sparkfun/SparkFun_RTK_mosaic-X5/docs/mining-onocoy.md

---
icon: fontawesome/solid/sack-dollar
status: new
---

Some RTK networks, such as [Onocoy](https://www.onocoy.com/), offer users incentives for operating a reference station and contributing RTK corrections to their network. These incentives are often tied to a form of cryptocurrency, which is rewarded based upon a performance scale after the data is validated.

!!! warning
	This section is for educational purposes only!

	This section doesn't contain nor should it be represented as an endorsement of any of the projects mentioned nor as financial advice. Don’t invest anything you aren’t willing to lose.

## Onocoy Documentation
Onocoy provides users with documentation for [mining rewards](https://docs.onocoy.com/documentation/quick-start-guides/mine-rewards) with an RTK reference station. To get started, users will need to have installed and mounted the hardware of their RTK mosaic-X5 and created a user account with Onocoy. Then, users can [obtain NTRIP server credentials from their account](https://docs.onocoy.com/documentation/quick-start-guides/mine-rewards/3.-connect-your-station-to-onocoy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), to connect their reference station to the Onocoy network.

<figure markdown>
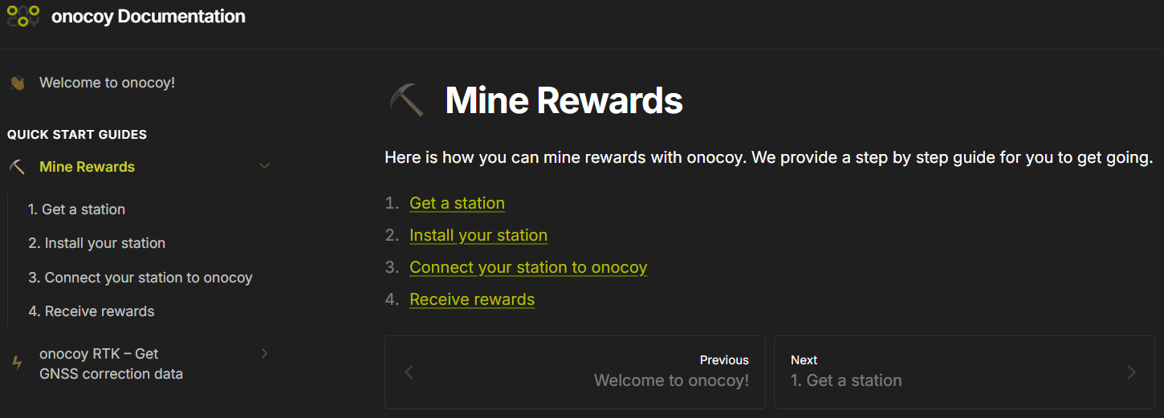
[picture p62: docs/assets/img/hookup_guide/onocoy-docs.png]
Onocoy documentaion

<figcaption markdown>Onocoy documentaion for [mining rewards](https://docs.onocoy.com/documentation/quick-start-guides/mine-rewards).</figcaption>
</figure>

## Configure the RTK mosaic-X5
In order to connect their RTK mosaic-X5 to the Onocoy network, users will need to adjust the configurations of the mosaic-X5 and setup an NTRIP server to the Onocoy network.

### :material-video-input-antenna: &nbsp;Enable L5 Band Reception
Before setting up the RTK mosaic-X5 as an NTRIP server, users will need to enable the GPS L5 frequency band in order to provide corrections for it. These steps, are documented in the [**Enable the L5 Band**](../L5/#l5-signal-reception) section of this tutorial:

<div class="grid cards" markdown>

-   **L5 Signal Reception**

	*Below, are instructions to enable the RTK mosaic-X5 to receive GNSS signals from the GPS L5 frequency band.*

	---

	--8<-- "./docs/L5.md:123:154"

</div>

### :material-router-network-wireless: &nbsp;Connect to the Onocoy Network
In order to connect the RTK mosaic-X5 to the Onocoy network, users will need to set up an NTRIP caster in the mosaic-X5 configuration settings. In order to receive the rewards, Onocoy expects a [specific set of configurations as listed in their online documentation](https://docs.onocoy.com/documentation/quick-start-guides/mine-rewards/3.-connect-your-station-to-onocoy).

<figure markdown>
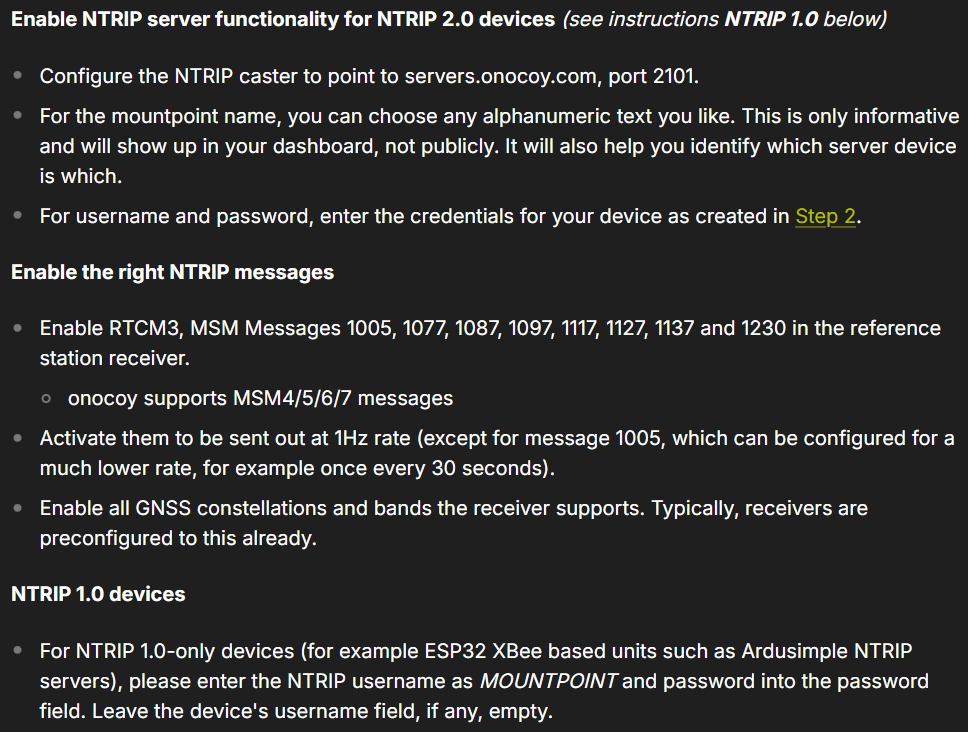
[picture p63: docs/assets/img/hookup_guide/onocoy-ntrip_settings.png]
NTRIP configuration settings

<figcaption markdown>The [specific parameters](https://docs.onocoy.com/documentation/quick-start-guides/mine-rewards/3.-connect-your-station-to-onocoy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) for connecting an NTRIP server to the Onocoy network, as listed in their documentation.</figcaption>
</figure>

Most of steps for these requirements, are documented in the [**Configure the NTRIP Server**](../ntrip_server/#configure-the-ntrip-server) section of this tutorial:

<div class="grid cards" markdown>

-   **Configure the NTRIP Server**

	---

	--8<-- "./docs/ntrip_server.md:49:55"

	??? failure "Ignore this information for this step"
		<s>
		--8<-- "./docs/ntrip_server.md:57:62"
		</s>

	!!! success
		Instead of the *confirmation email*, use the information provided in the [Onocoy documentation](https://docs.onocoy.com/documentation/quick-start-guides/mine-rewards/3.-connect-your-station-to-onocoy):

		> - Configure the NTRIP caster to point to `servers.onocoy.com`, port `2101`.
		> - For the `mountpoint` name, you can choose any alphanumeric text you like. This is only informative and will show up in your dashboard, not publicly. It will also help you identify which server device is which.
		> - For `username` and `password`, enter the credentials for your device as created in [Step 2](https://docs.onocoy.com/documentation/quick-start-guides/mine-rewards/3.-connect-your-station-to-onocoy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).

		<figure markdown>
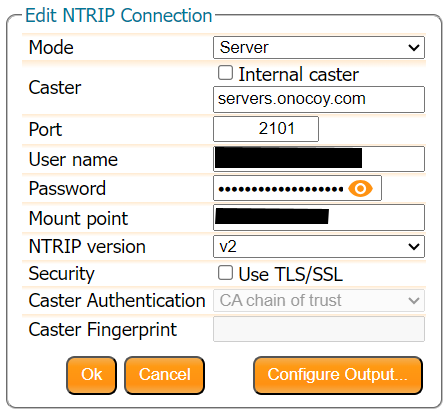
[picture p64: docs/assets/img/hookup_guide/onocoy-ntrip_server.png]
Configuring the NTRIP server
		
		<figcaption markdown>[Configuring the NTRIP server (PNG)](./assets/img/hookup_guide/onocoy-ntrip_server.png).</figcaption>
		</figure>

	--8<-- "./docs/ntrip_server.md:64:69"

	??? failure "Ignore this information for this step"
		<s>
		--8<-- "./docs/ntrip_server.md:71:76"
		</s>

	!!! success
		Instead, also select the RTCM messages listed in the [Onocoy documentation](https://docs.onocoy.com/documentation/quick-start-guides/mine-rewards/3.-connect-your-station-to-onocoy). Below, are the RTCM messages we selected:

		> - Enable RTCM3, MSM Messages `1005`, `1077`, `1087`, `1097`, `1117`, `1127`, `1137`, and `1230` in the reference station receiver.
		> - onocoy supports MSM4/5/6/7 messages

		<figure markdown>
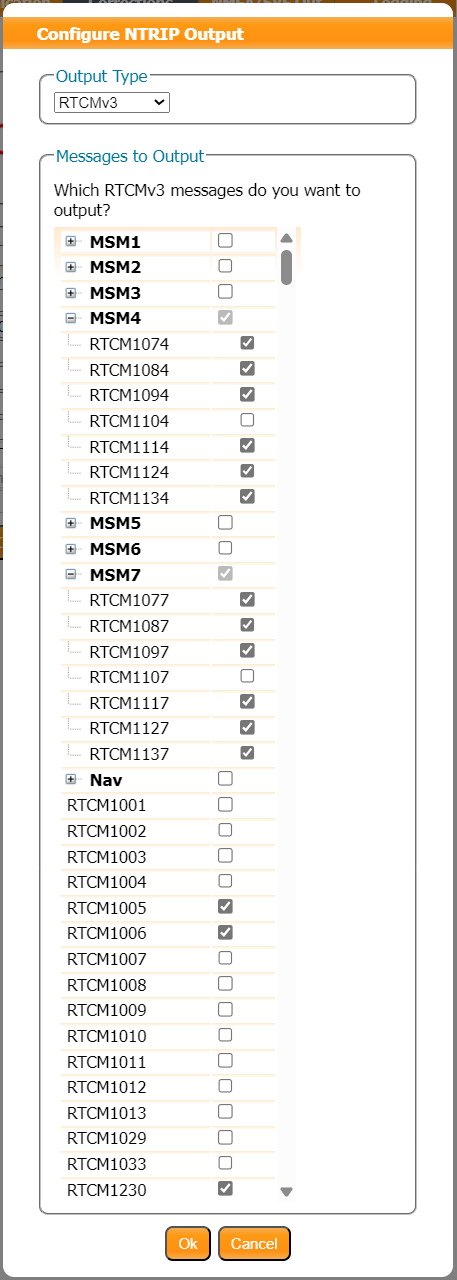
[picture p65: docs/assets/img/hookup_guide/onocoy-rtcm_messages.png]
RTCMv3 messages
		
		<figcaption markdown>[RTCMv3 messages (PNG)](./assets/img/hookup_guide/onocoy-rtcm_messages.png).</figcaption>
		</figure>

	--8<-- "./docs/ntrip_server.md:78:79"

</div>

### :fontawesome-solid-map-location-dot: &nbsp;Enable L5 Corrections
The last step in configuring the NTRIP server, users will need to enable the GPS L5 signal to be included in the MSM output messages. This will allow the RTK mosaic-X5 to provide RTK corrections for the GPS L5 frequency band. These steps, are documented in the [**Output L5 Corrections**](../L5/#output-l5-corrections) section of this tutorial:

<div class="grid cards" markdown>

-   **Output L5 Corrections**

	*Below, are instructions for outputting RTK corrections for the GPS L5 frequency band, from the RTK mosaic-X5.*

	---

	--8<-- "./docs/L5.md:167"

</div>

## :fontawesome-solid-money-bill-trend-up: &nbsp;Receive Rewards
Once users have connected the RTK mosaic-X5 as an NTRIP server on the Onocoy network, there are a few additional steps in that need to be completed, a specified in their [online documentation](https://docs.onocoy.com/documentation/quick-start-guides/mine-rewards/4.-receive-rewards).

<article style="text-align: center;" markdown>
:material-pickaxe::material-gold:&nbsp; Happy Mining! :material-pickaxe::material-gold:
</article>
