sparkfun/SparkFun_RTK_mosaic-X5/Front_Panel/RTK_mosaic-X5_Front_Panel.png

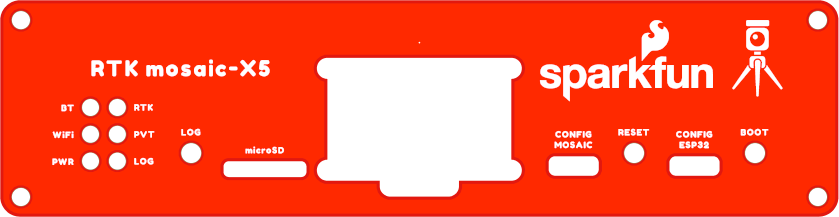
Front_Panel/RTK_mosaic-X5_Front_Panel.png
