sparkfun/SparkFun_RTK_mosaic-X5/Rear_Panel/RTK_mosaic-X5_Rear_Panel.png

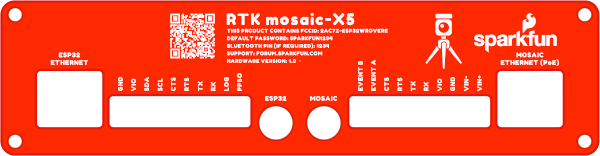
Rear_Panel/RTK_mosaic-X5_Rear_Panel.png
