sparkfun/SparkFun_RTK_mosaic-X5/docs/assets/img/hookup_guide/Log.jpg

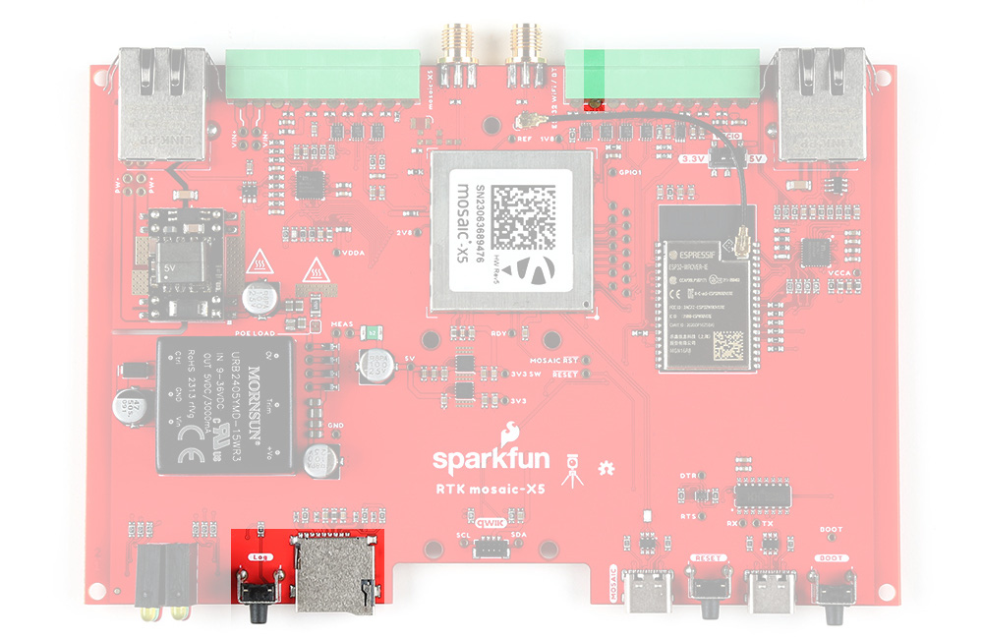
docs/assets/img/hookup_guide/Log.jpg
