sparkfun/SparkFun_RTK_mosaic-X5/docs/assets/img/hookup_guide/OLED2.png

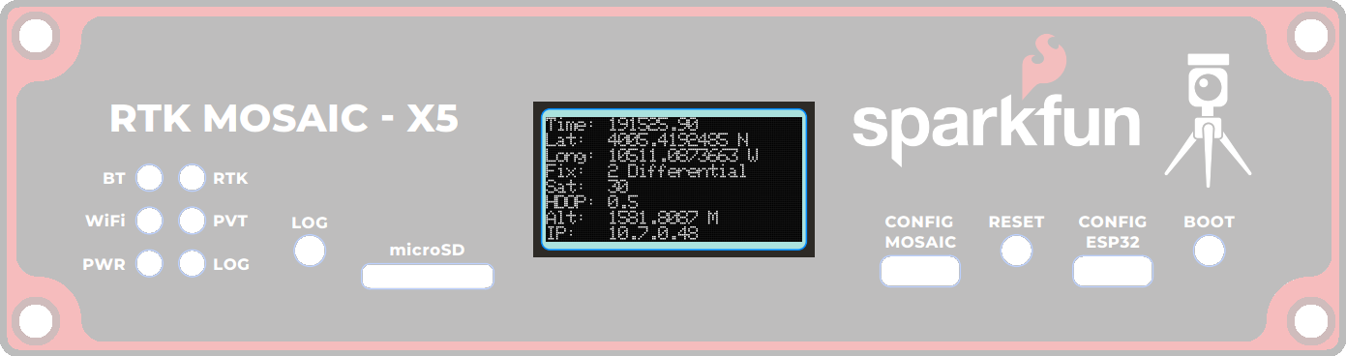
docs/assets/img/hookup_guide/OLED2.png
