sparkfun/SparkFun_RTK_mosaic-X5/docs/assets/img/hookup_guide/panel-front.png

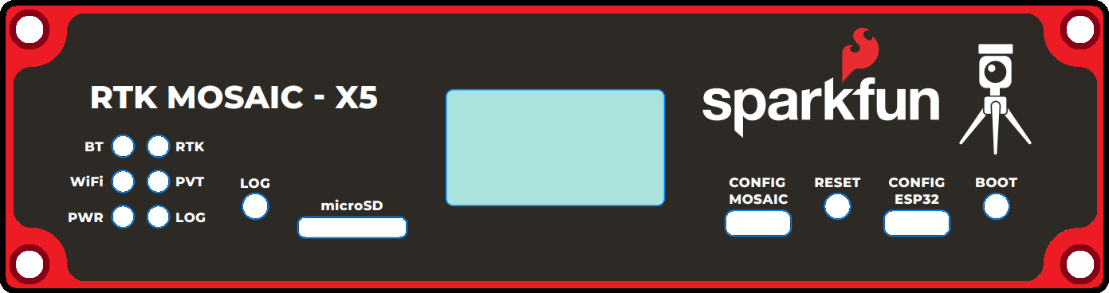
docs/assets/img/hookup_guide/panel-front.png
