sparkfun/SparkFun_RTK_mosaic-X5/docs/assets/img/hookup_guide/panel-rear.png

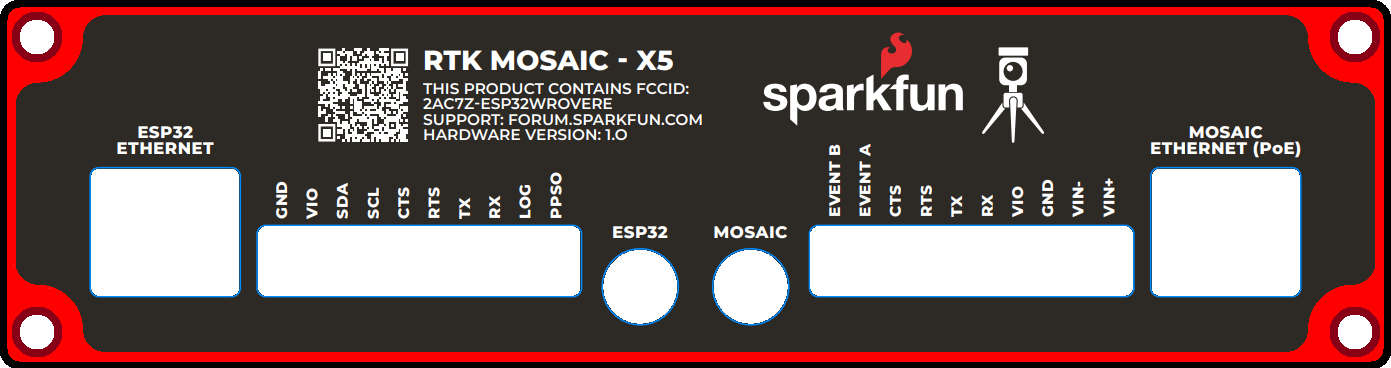
docs/assets/img/hookup_guide/panel-rear.png
