sparkfun/SparkFun_RTK_mosaic-X5/docs/assets/img/hookup_guide/PCB_Bottom.png

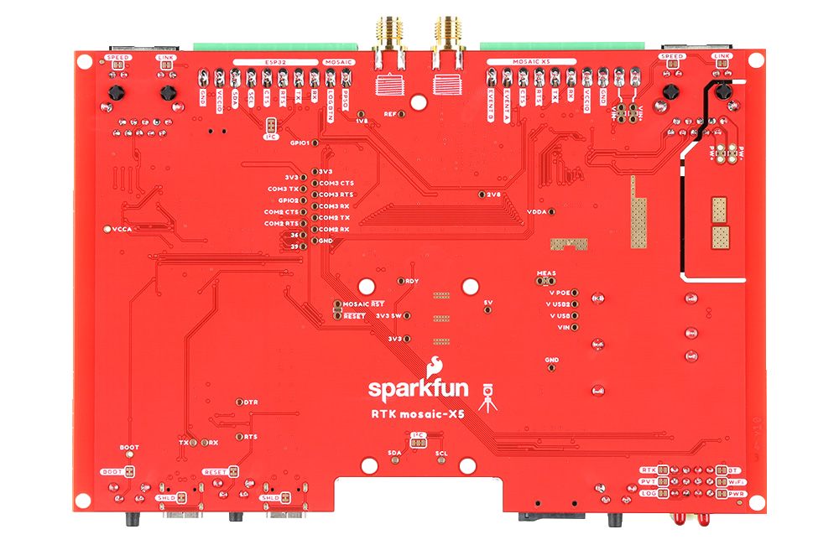
docs/assets/img/hookup_guide/PCB_Bottom.png
