sparkfun/SparkFun_RTK_mosaic-X5/docs/assets/img/hookup_guide/template_OLED-info.png

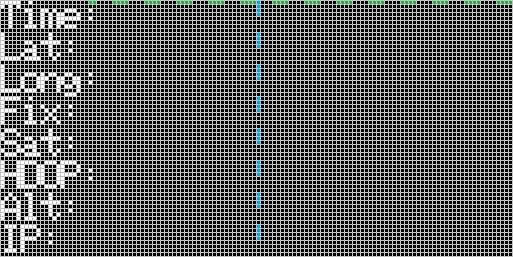
docs/assets/img/hookup_guide/template_OLED-info.png
