sparkfun/SparkFun_RTK_mosaic-X5/docs/assets/component_documentation/mowi_schematic_MERGED.pdf

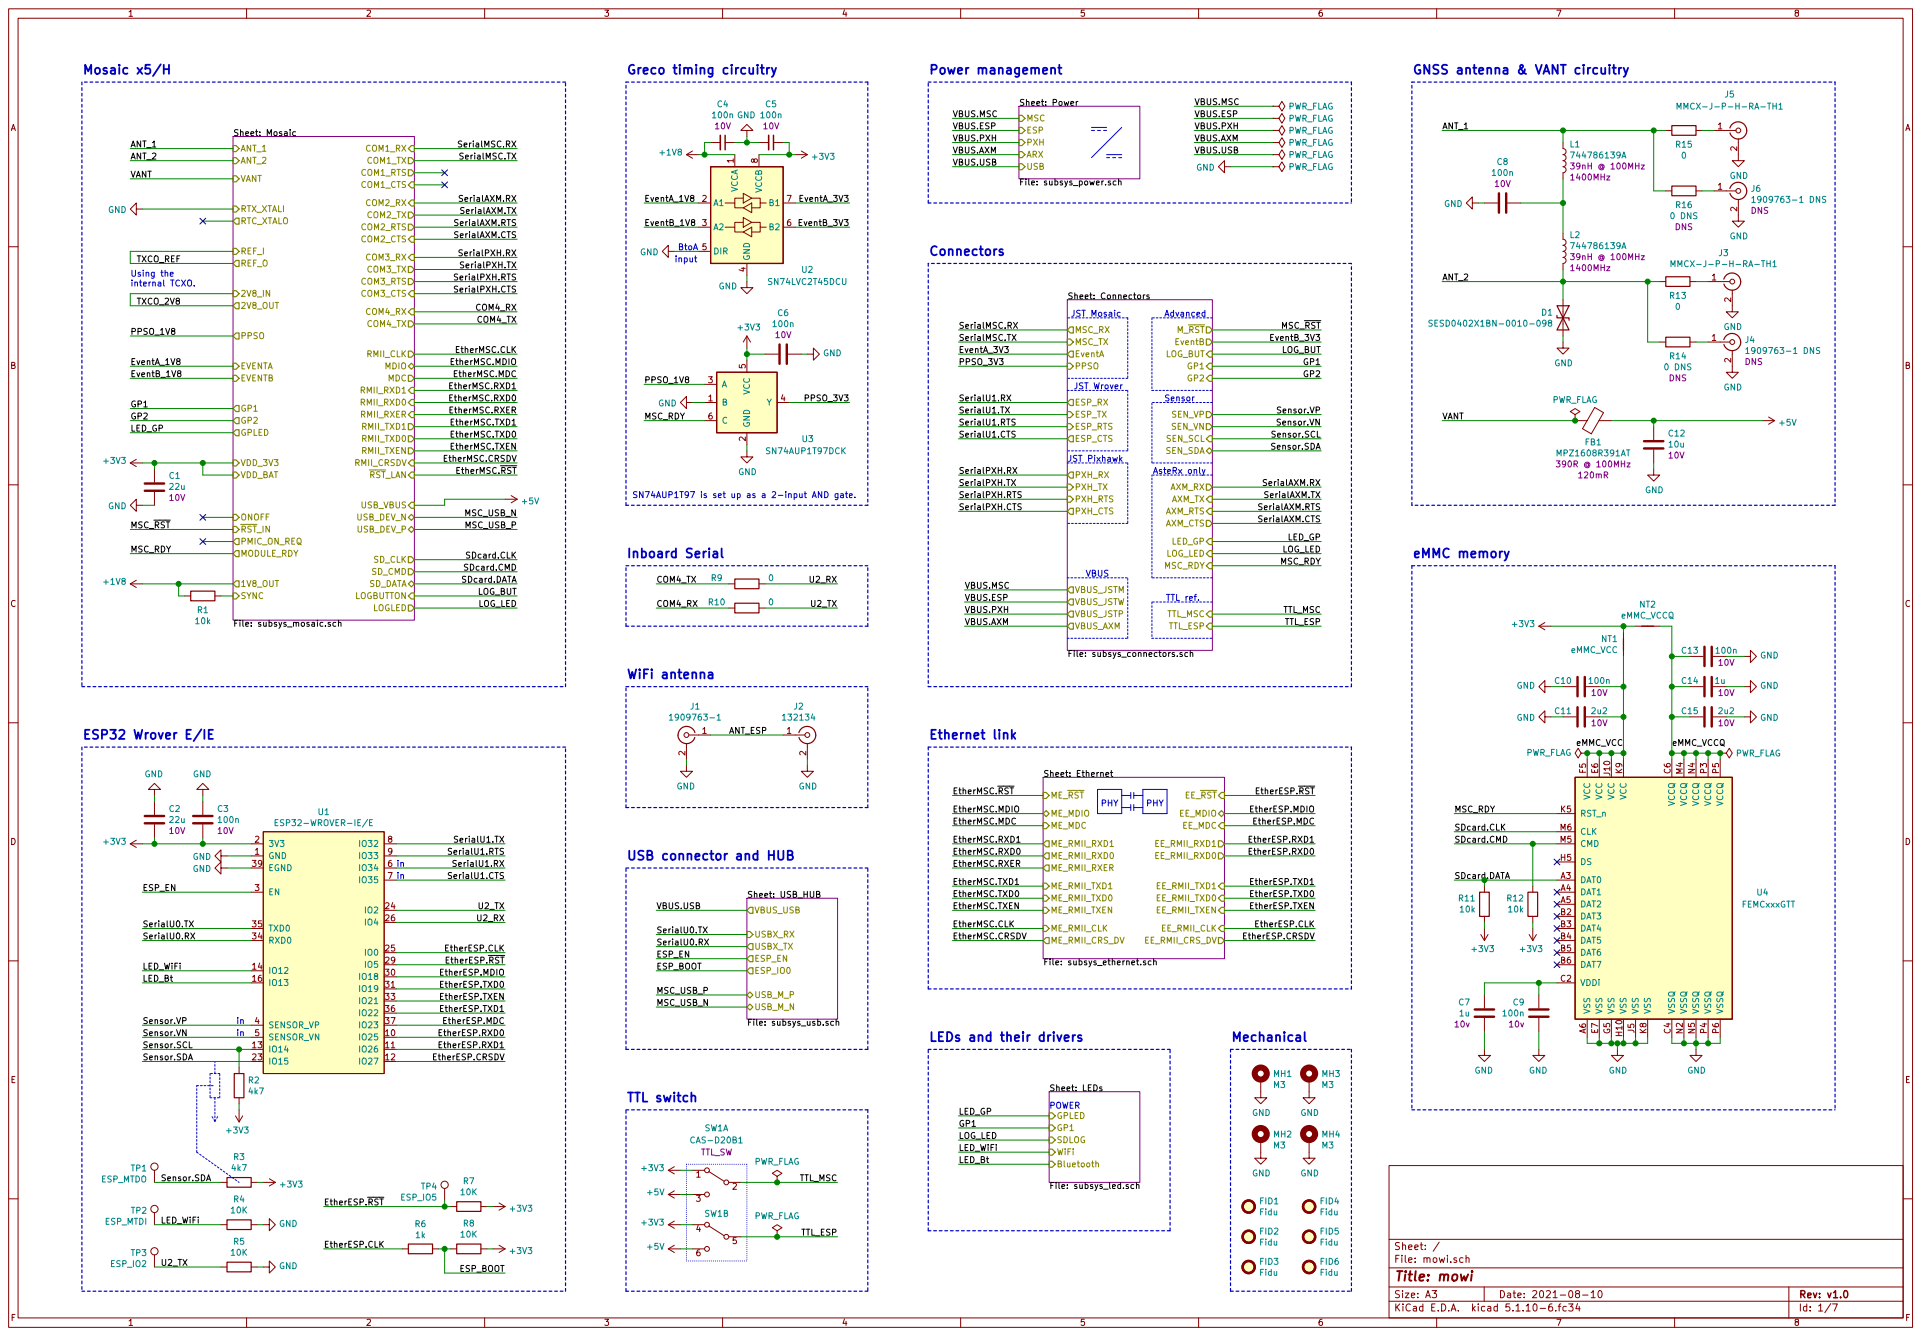
[picture p147: page 1]

Sheet: Mosaic File: subsys_mosaic.sch VDD_3V3 VDD_BAT REF_I 2V8_IN
VANT ANT_2 ANT_1 RTX_XTALI ONOFF RST_IN
COM4_TX COM3_RTS COM3_TX COM2_RTS COM2_TX COM1_RTS COM1_TX

GNSS antenna & VANT circuitry

Sheet: Power File: subsys_power.sch MSC

8 U2 SN74LVC2T45DCU
Advanced AsteRx only VBUS

J3 MMCX-J-P-H-RA-TH1 GND GND

SN74AUP1T97 is set up as a 2-input AND gate.
ESP_BOOT COM4_TX

TTL_MSC
TTL_ESP
Sheet: Ethernet File: subsys_ethernet.sch ME_RMII_TXEN ME_RMII_TXD0 ME_RMII_TXD1 ME_RMII_CLK
EtherESP.RST EtherESP.CRSDV

USB connector and HUB

EtherESP.RST EtherESP.MDC
EtherESP.MDIO

Sensor.VP
Sensor.SCL Sensor.VN

EtherESP.RXD1 EtherESP.RXD0 EtherESP.CRSDV

LEDs and their drivers

Sheet: LEDs File: subsys_led.sch Bluetooth WiFi GP1 GPLED

Id: 1/7 Title: mowi File: mowi.sch Sheet: /

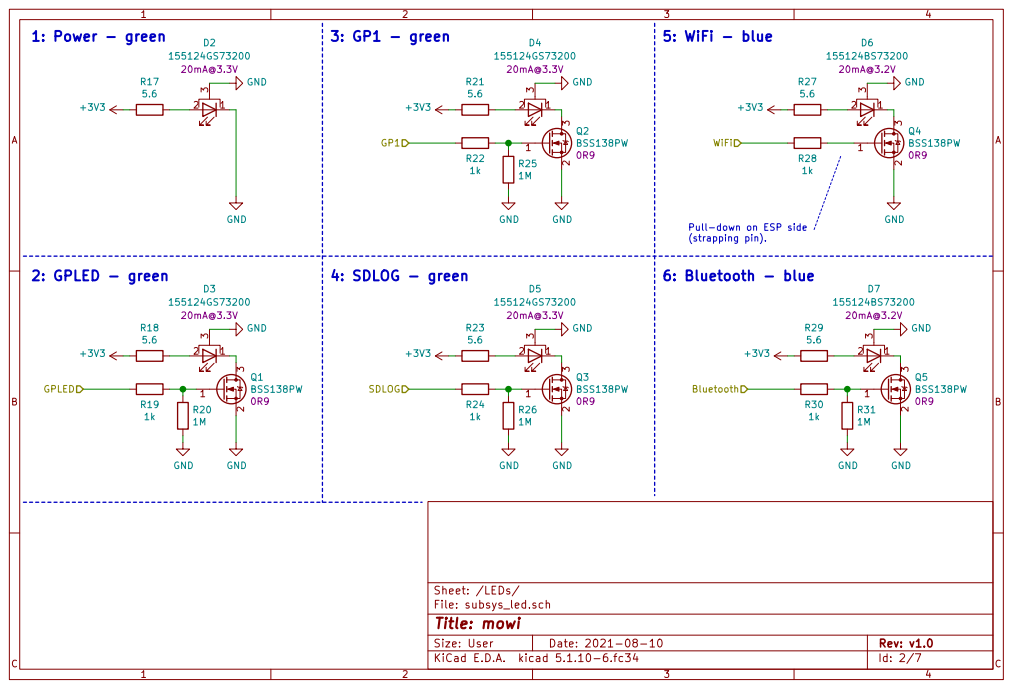
[picture p148: page 2]

Pull-down on ESP side
(strapping pin).

File: subsys_led.sch Sheet: /LEDs/ R19

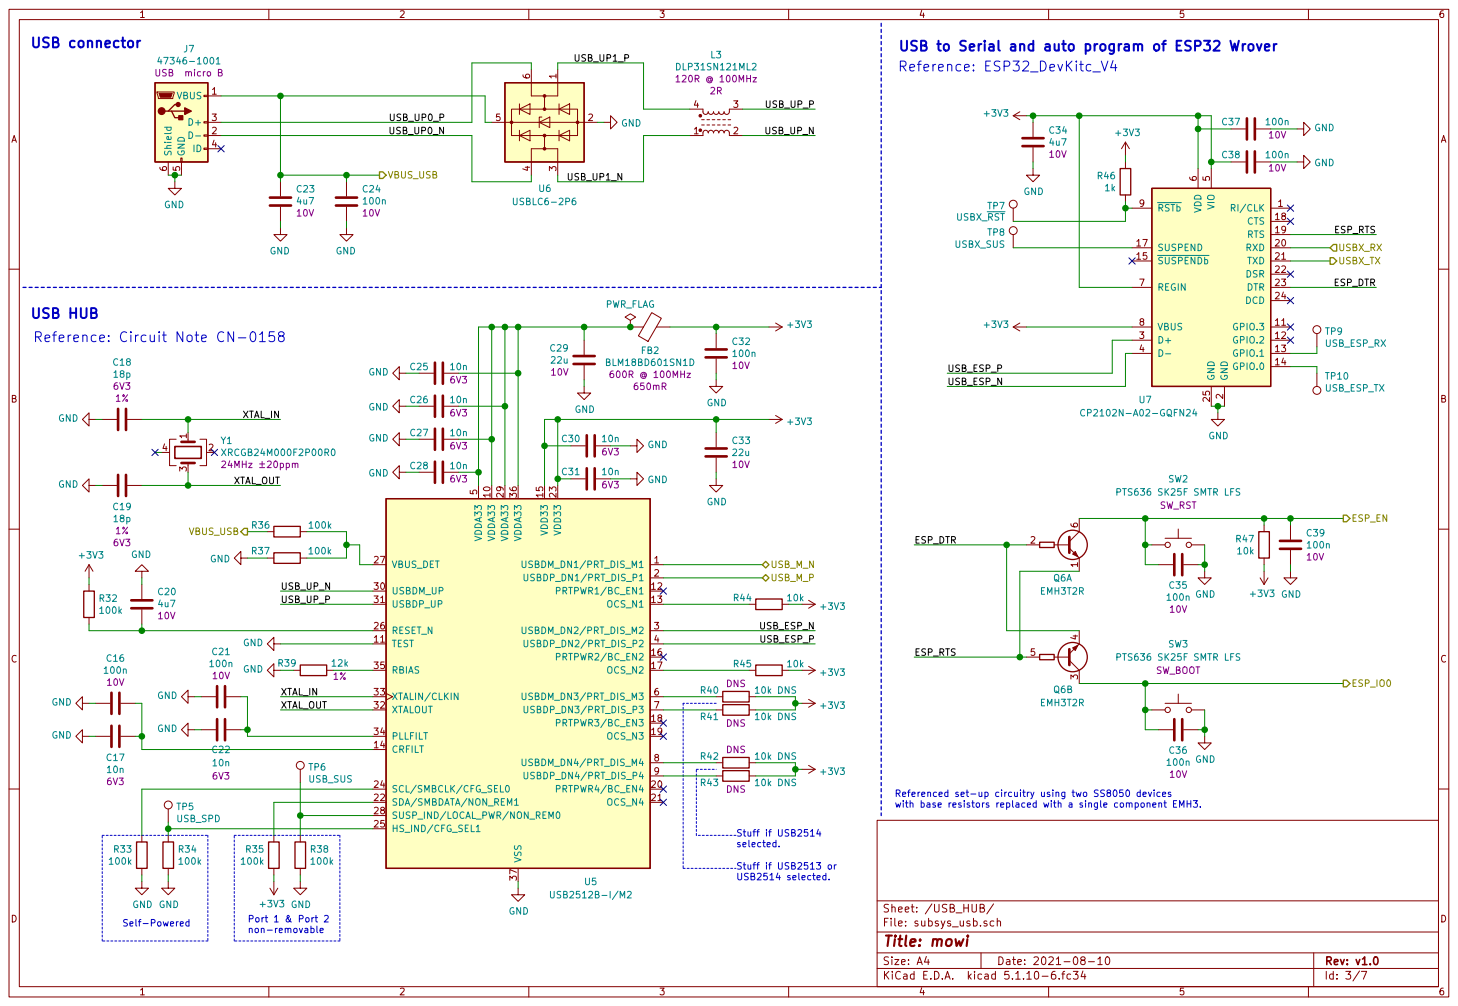
[picture p149: page 3]

non-removable Reference: Circuit Note CN-0158

6 REGIN 7 VBUS 8 RSTb 9U7 CP2102N-A02-GQFN24 GND

2 RXD 20 TXD 21 DSR 22 DTR 23 DCD 24 GND 25 D+ 3 D- 4 VIO

Referenced set-up circuitry using two SS8050 devices
with base resistors replaced with a single component EMH3.

Stuff if USB2513 or USB2514 selected.

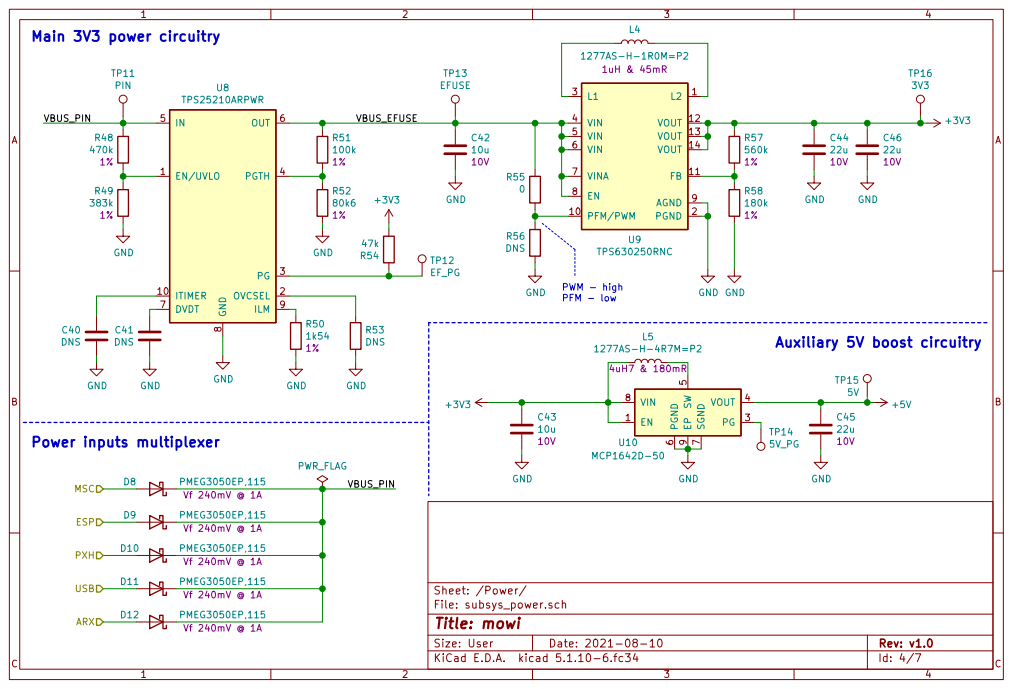
[picture p150: page 4]

PWM - high PFM - low Power inputs multiplexer

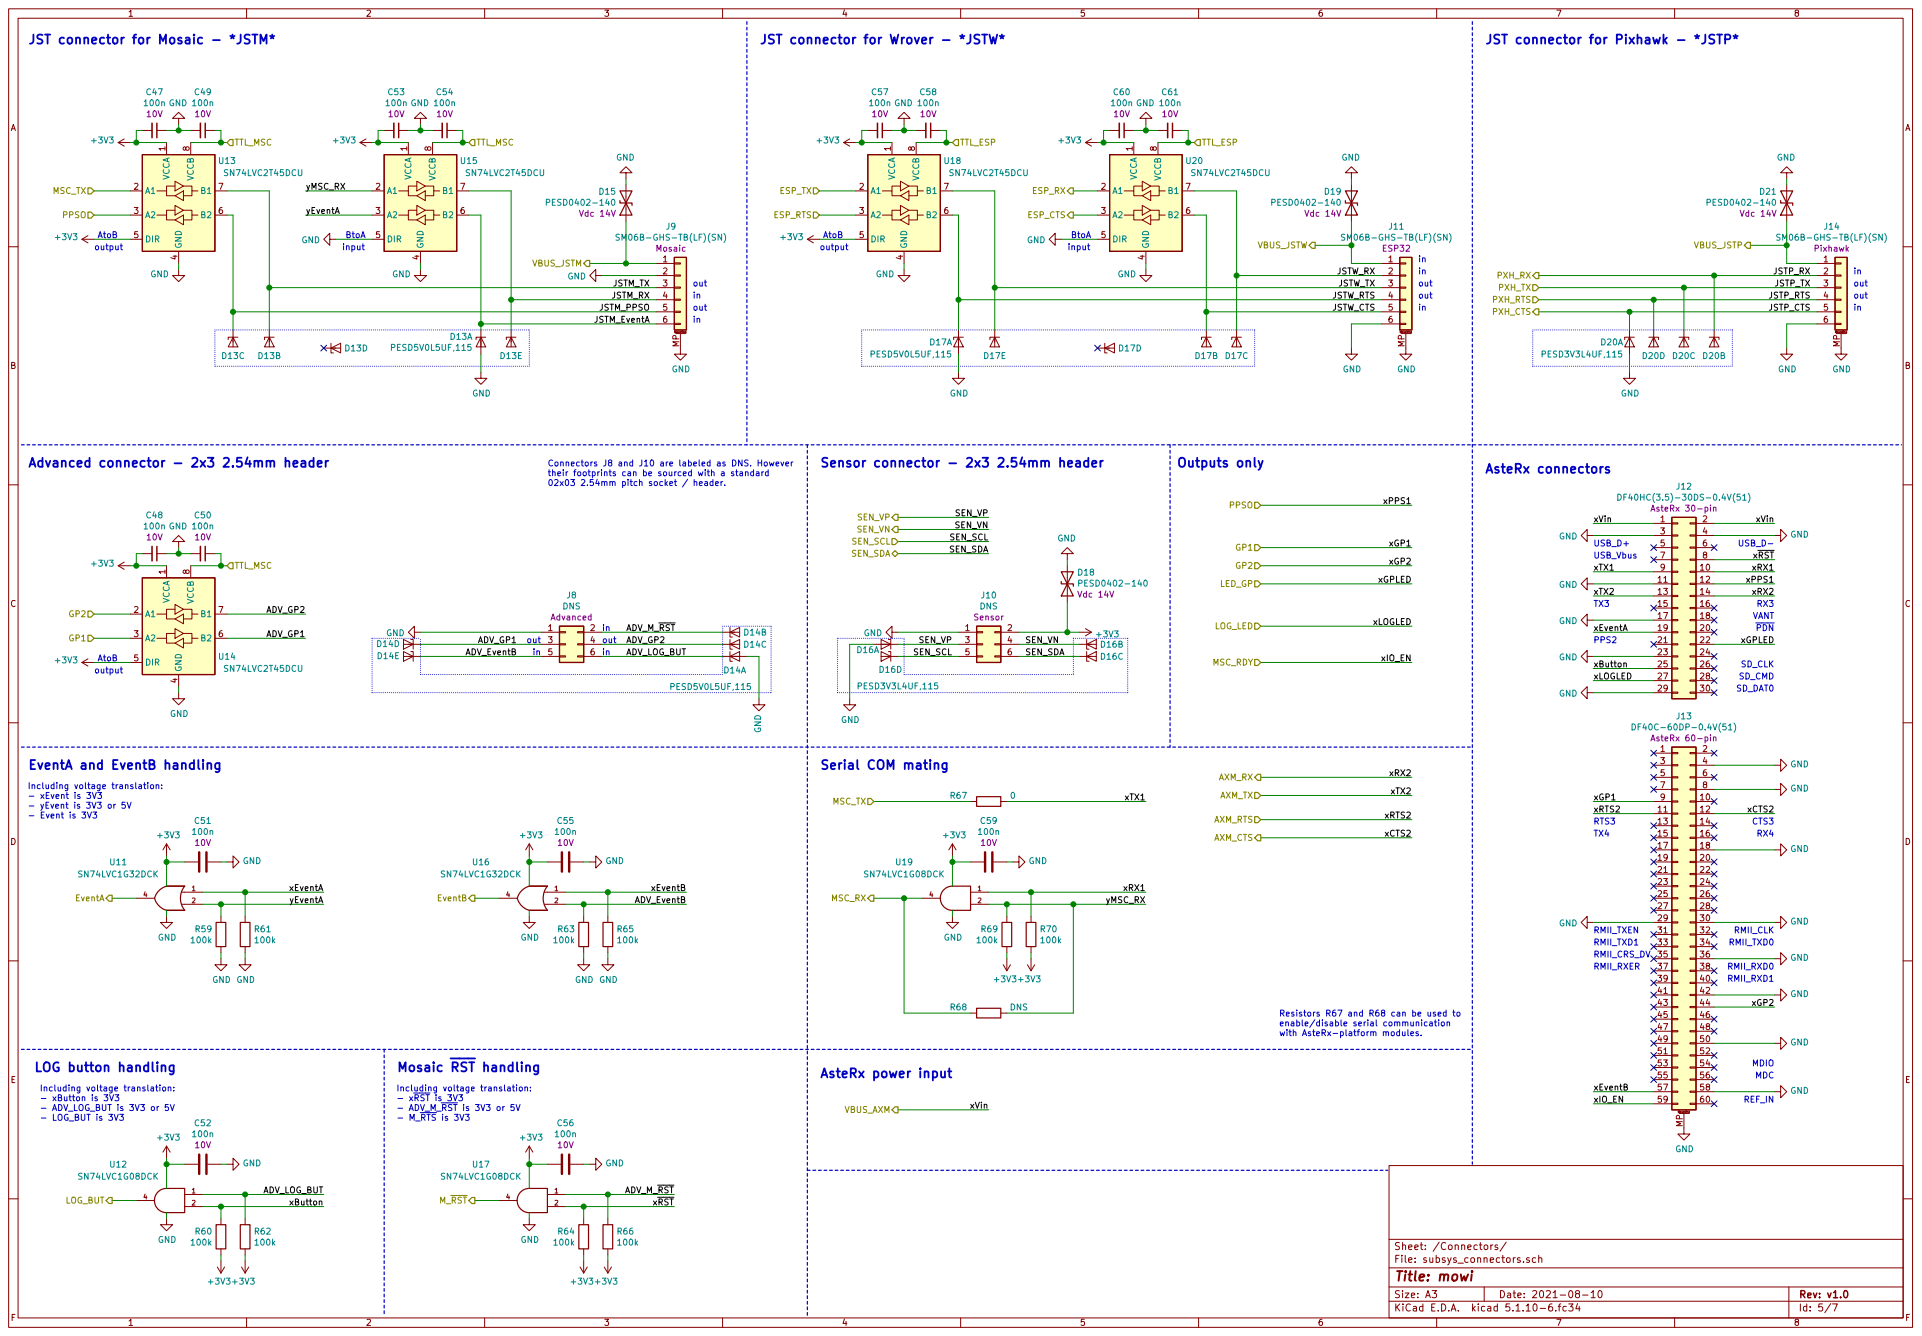
[picture p151: page 5]

JST connector for Mosaic - *JSTM*

JST connector for Pixhawk - *JSTP*

J14 SM06B-GHS-TB(LF)(SN) Pixhawk

02x03 2.54mm pitch socket / header. BtoA
input

out LOG button handling

AsteRx 60-pin GND GND

in Advanced connector - 2x3 2.54mm header AtoB

Connectors J8 and J10 are labeled as DNS. However
their footprints can be sourced with a standard

EventA and EventB handling

Including voltage translation: - xEvent is 3V3

enable/disable serial communication with AsteRx-platform modules.

Including voltage translation: - xButton is 3V3

Including voltage translation: - xRST is 3V3

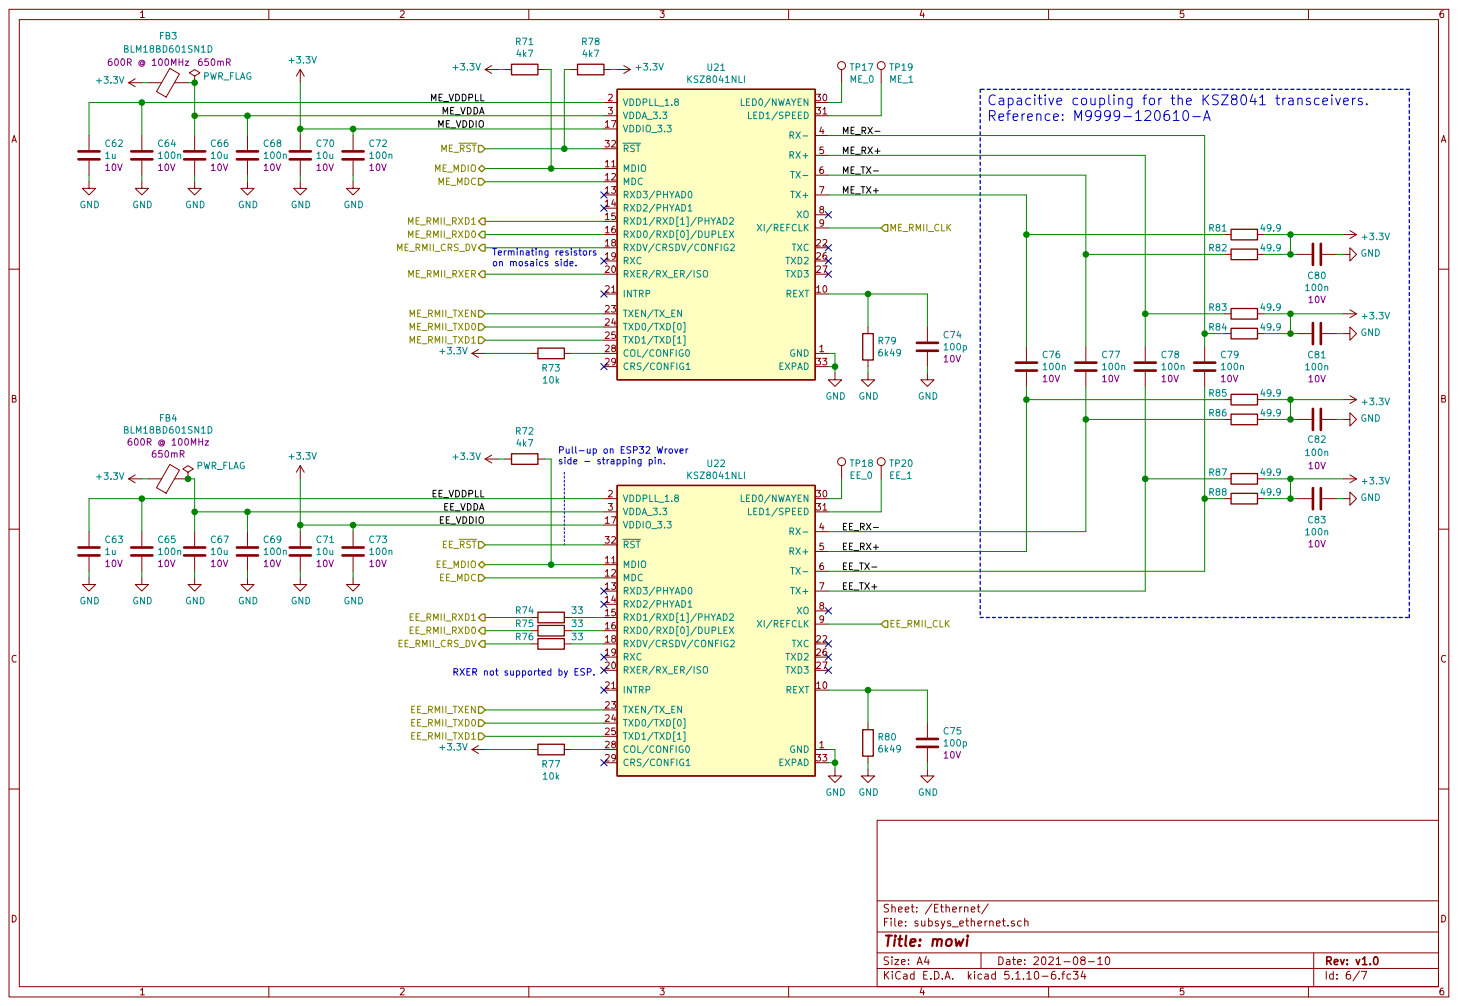
[picture p152: page 6]

EE_RST ME_MDC ME_RMII_CRS_DV ME_RMII_TXD0 ME_RMII_RXD1 ME_RMII_RXD0 ME_RMII_RXER ME_RST ME_RMII_TXEN ME_RMII_TXD1 EE_RMII_CRS_DV
Terminating resistors on mosaics side. RXER not supported by ESP.

Capacitive coupling for the KSZ8041 transceivers.
Reference: M9999-120610-A

EE_RX- EE_RX+ EE_TX- ME_TX- Pull-up on ESP32 Wrover

File: subsys_ethernet.sch Sheet: /Ethernet/ GND

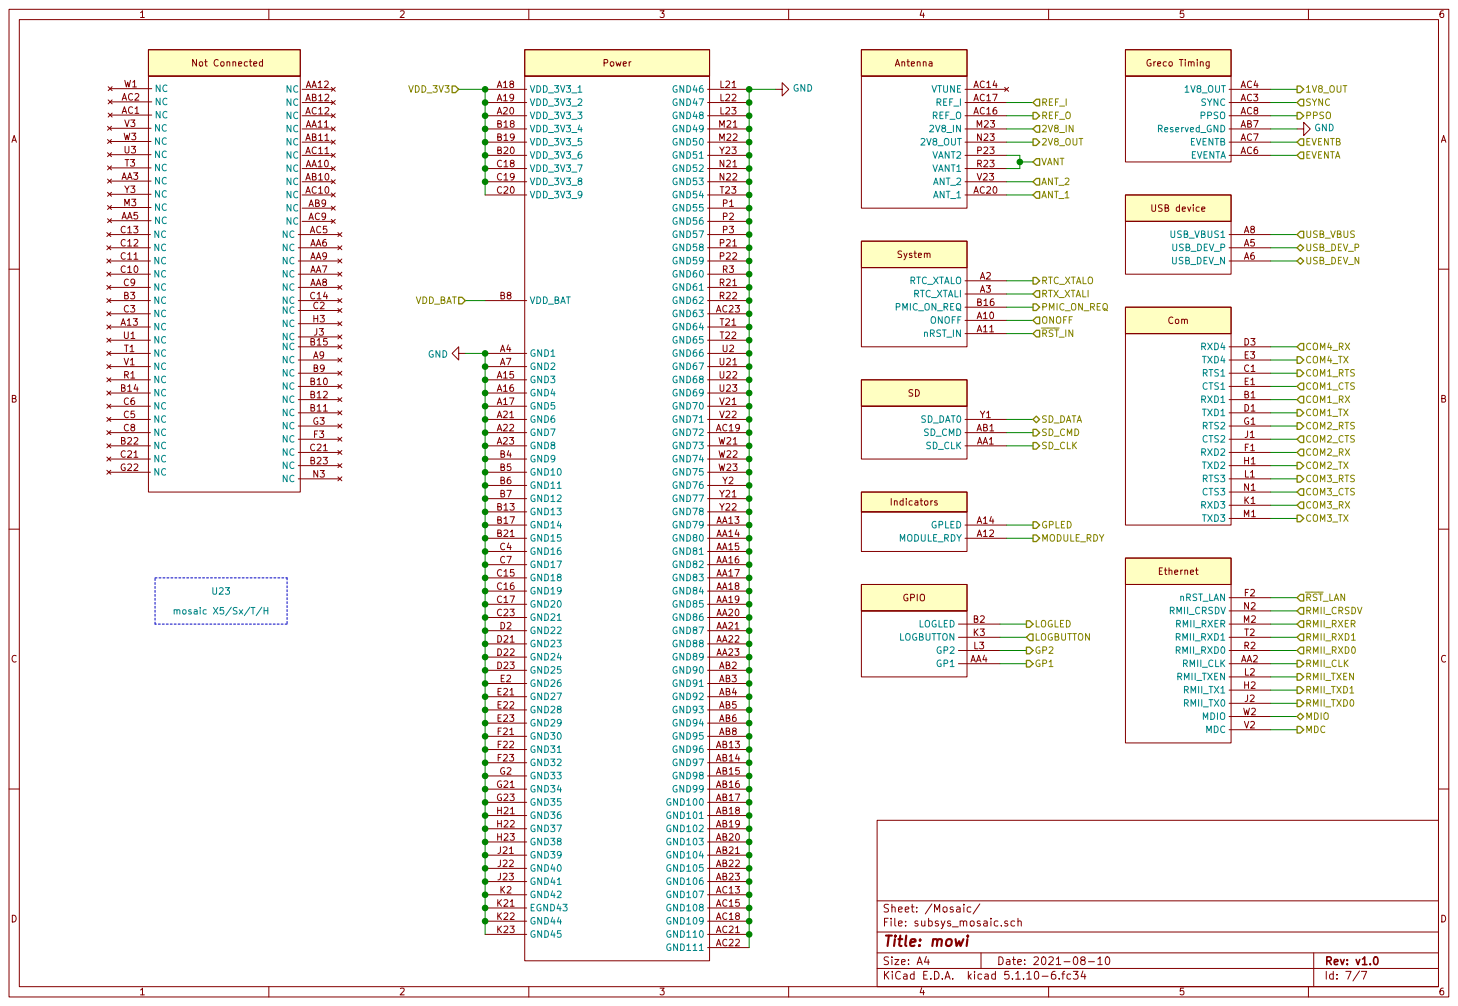
[picture p153: page 7]

File: subsys_mosaic.sch Sheet: /Mosaic/
Id: 7/7 Title: mowi
