sparkfun/SparkFun_RTK_mosaic-X5/docs/assets/board_files/dimensions.pdf

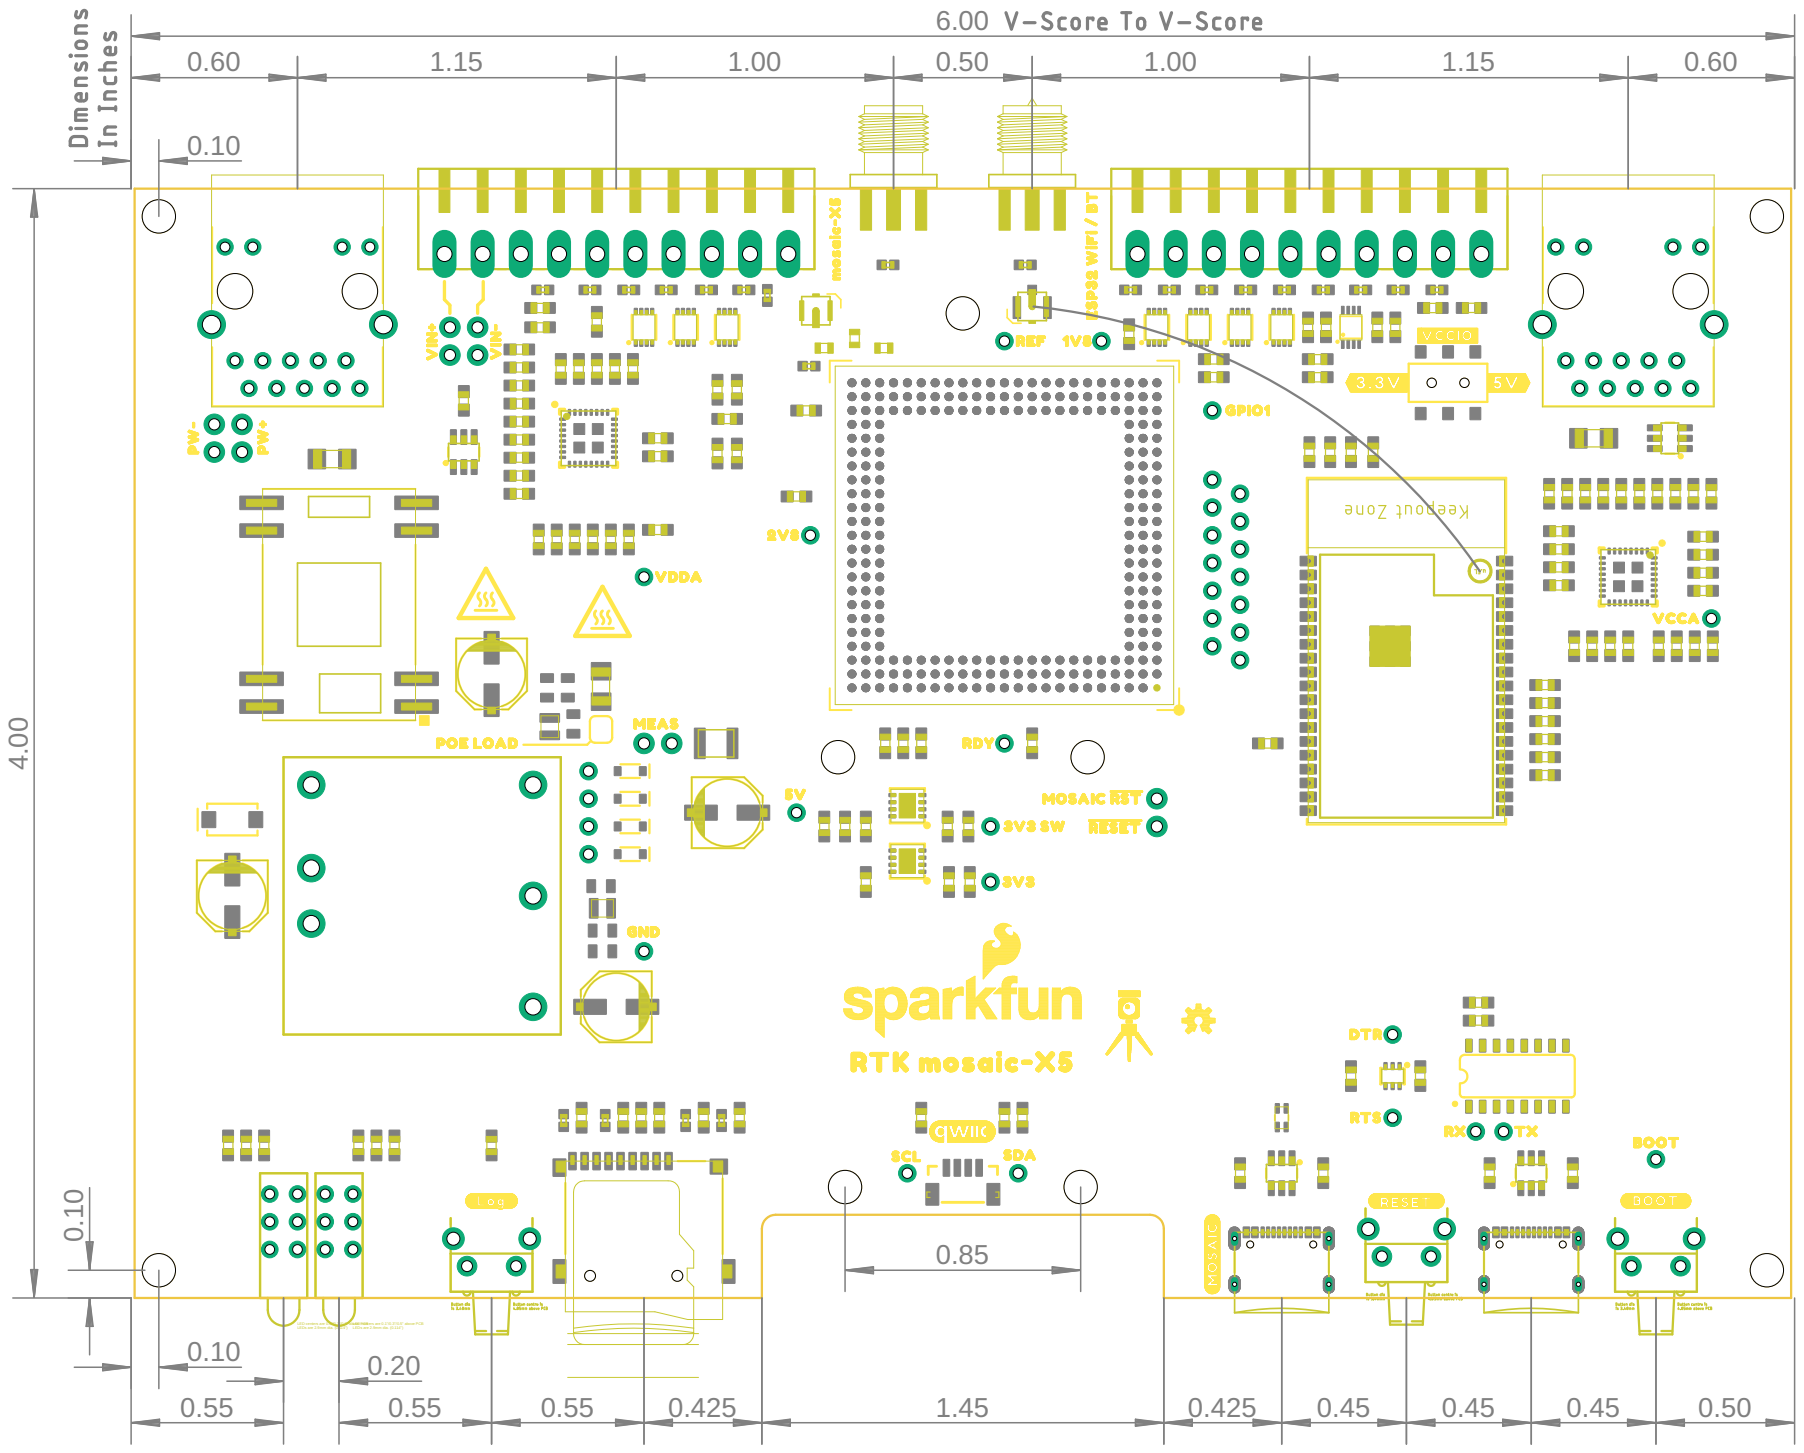
[picture p154: page 1]

LED centers are 0.1"/0.3"/0.5" above PCB
