sparkfun/SparkFun_RTK_mosaic-X5/docs/assets/board_files/dimension-front_panel.pdf

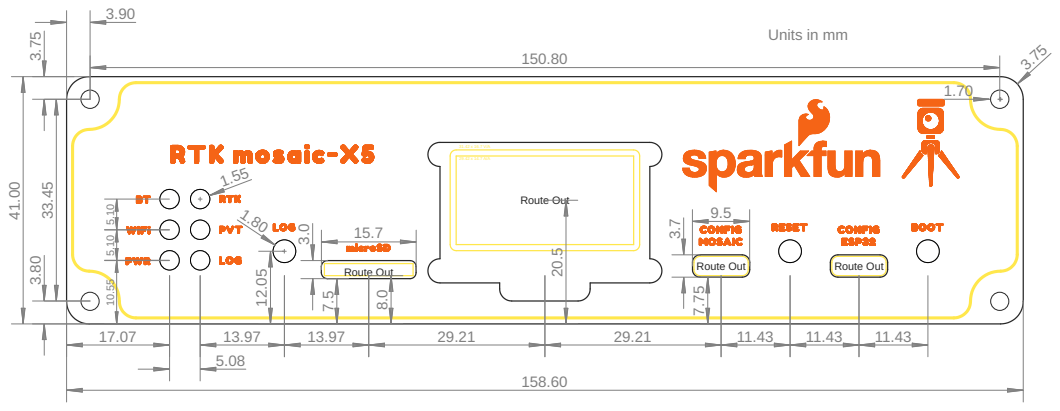
[picture p155: page 1]
