sparkfun/SparkFun_RTK_mosaic-X5/docs/assets/board_files/dimension-panels.pdf

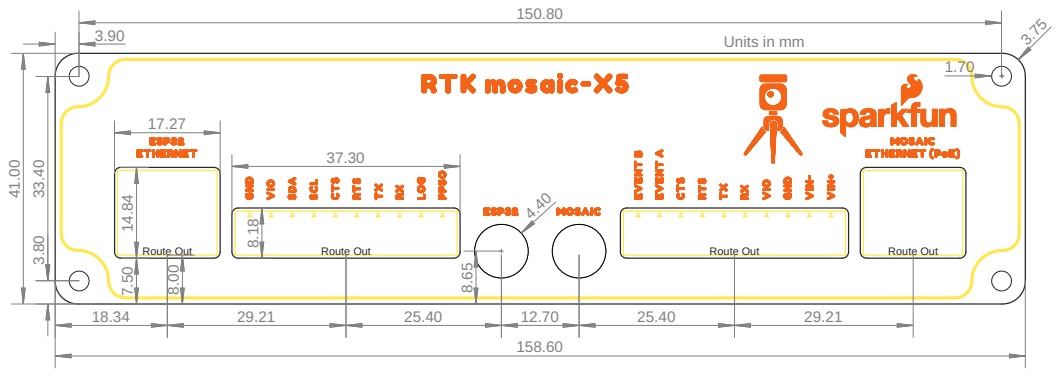
[picture p156: page 2]
