sparkfun/SparkFun_RTK_mosaic-X5/docs/assets/board_files/dimensions-enclosure.pdf

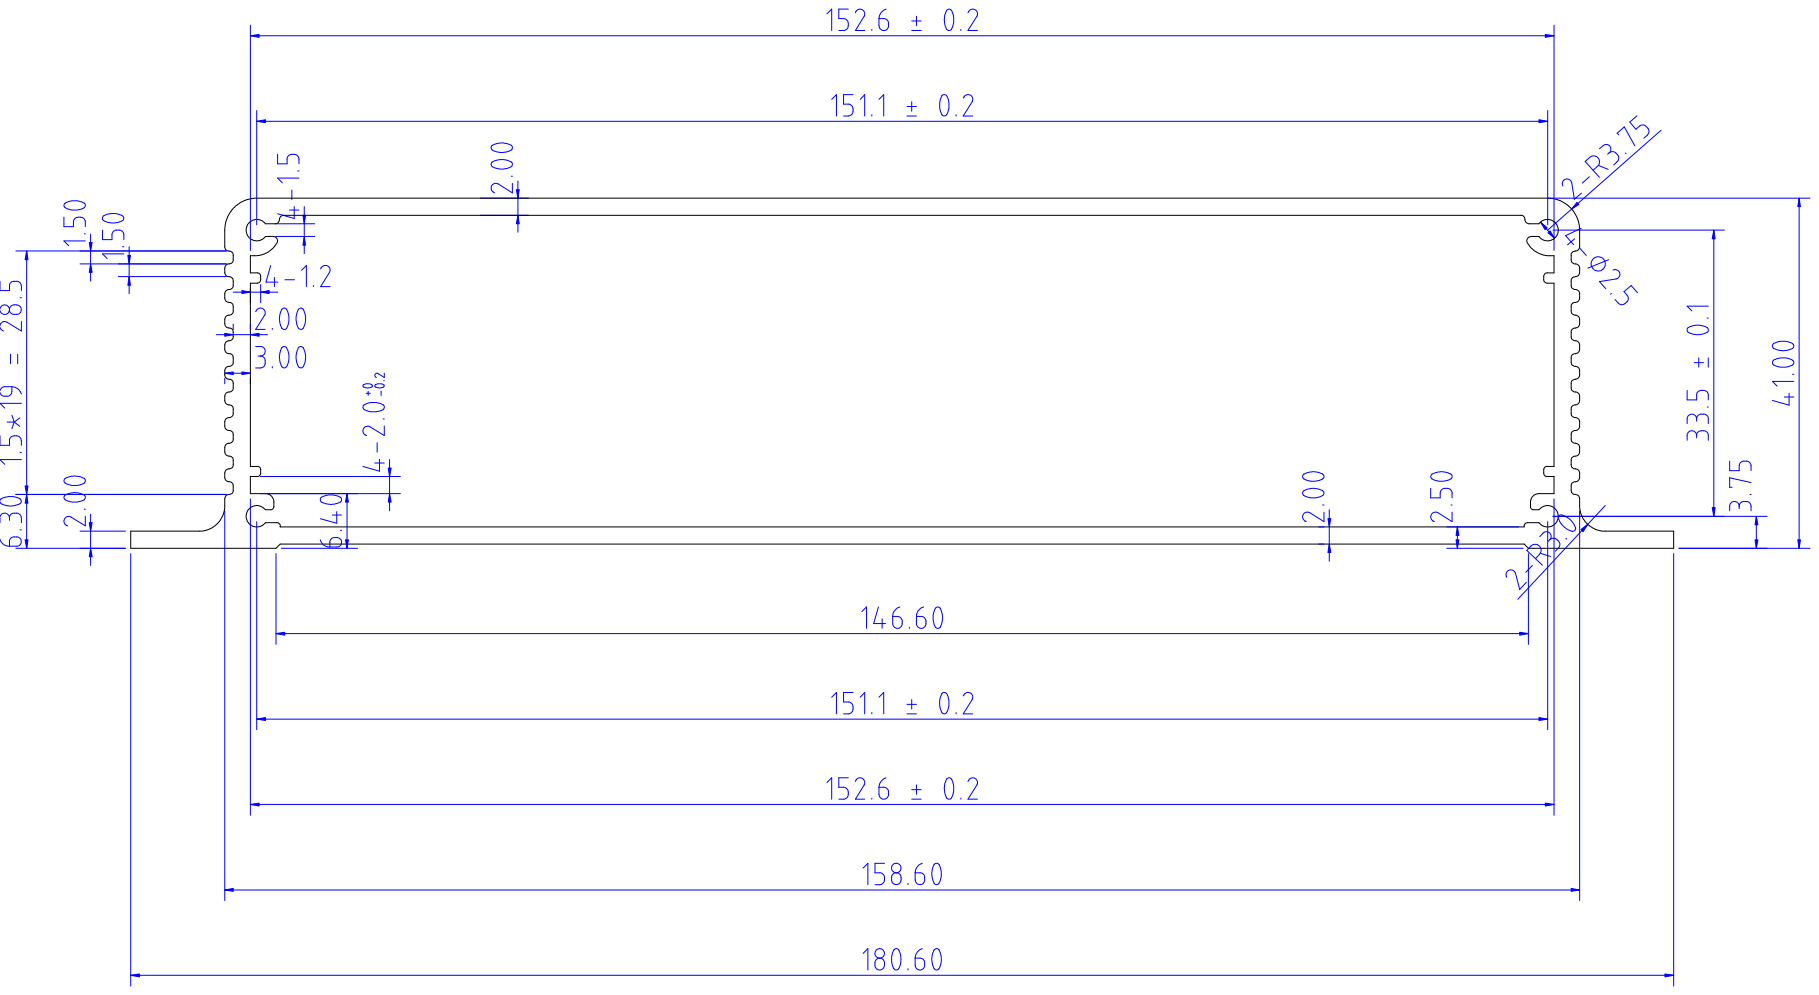
[picture p157: page 1]

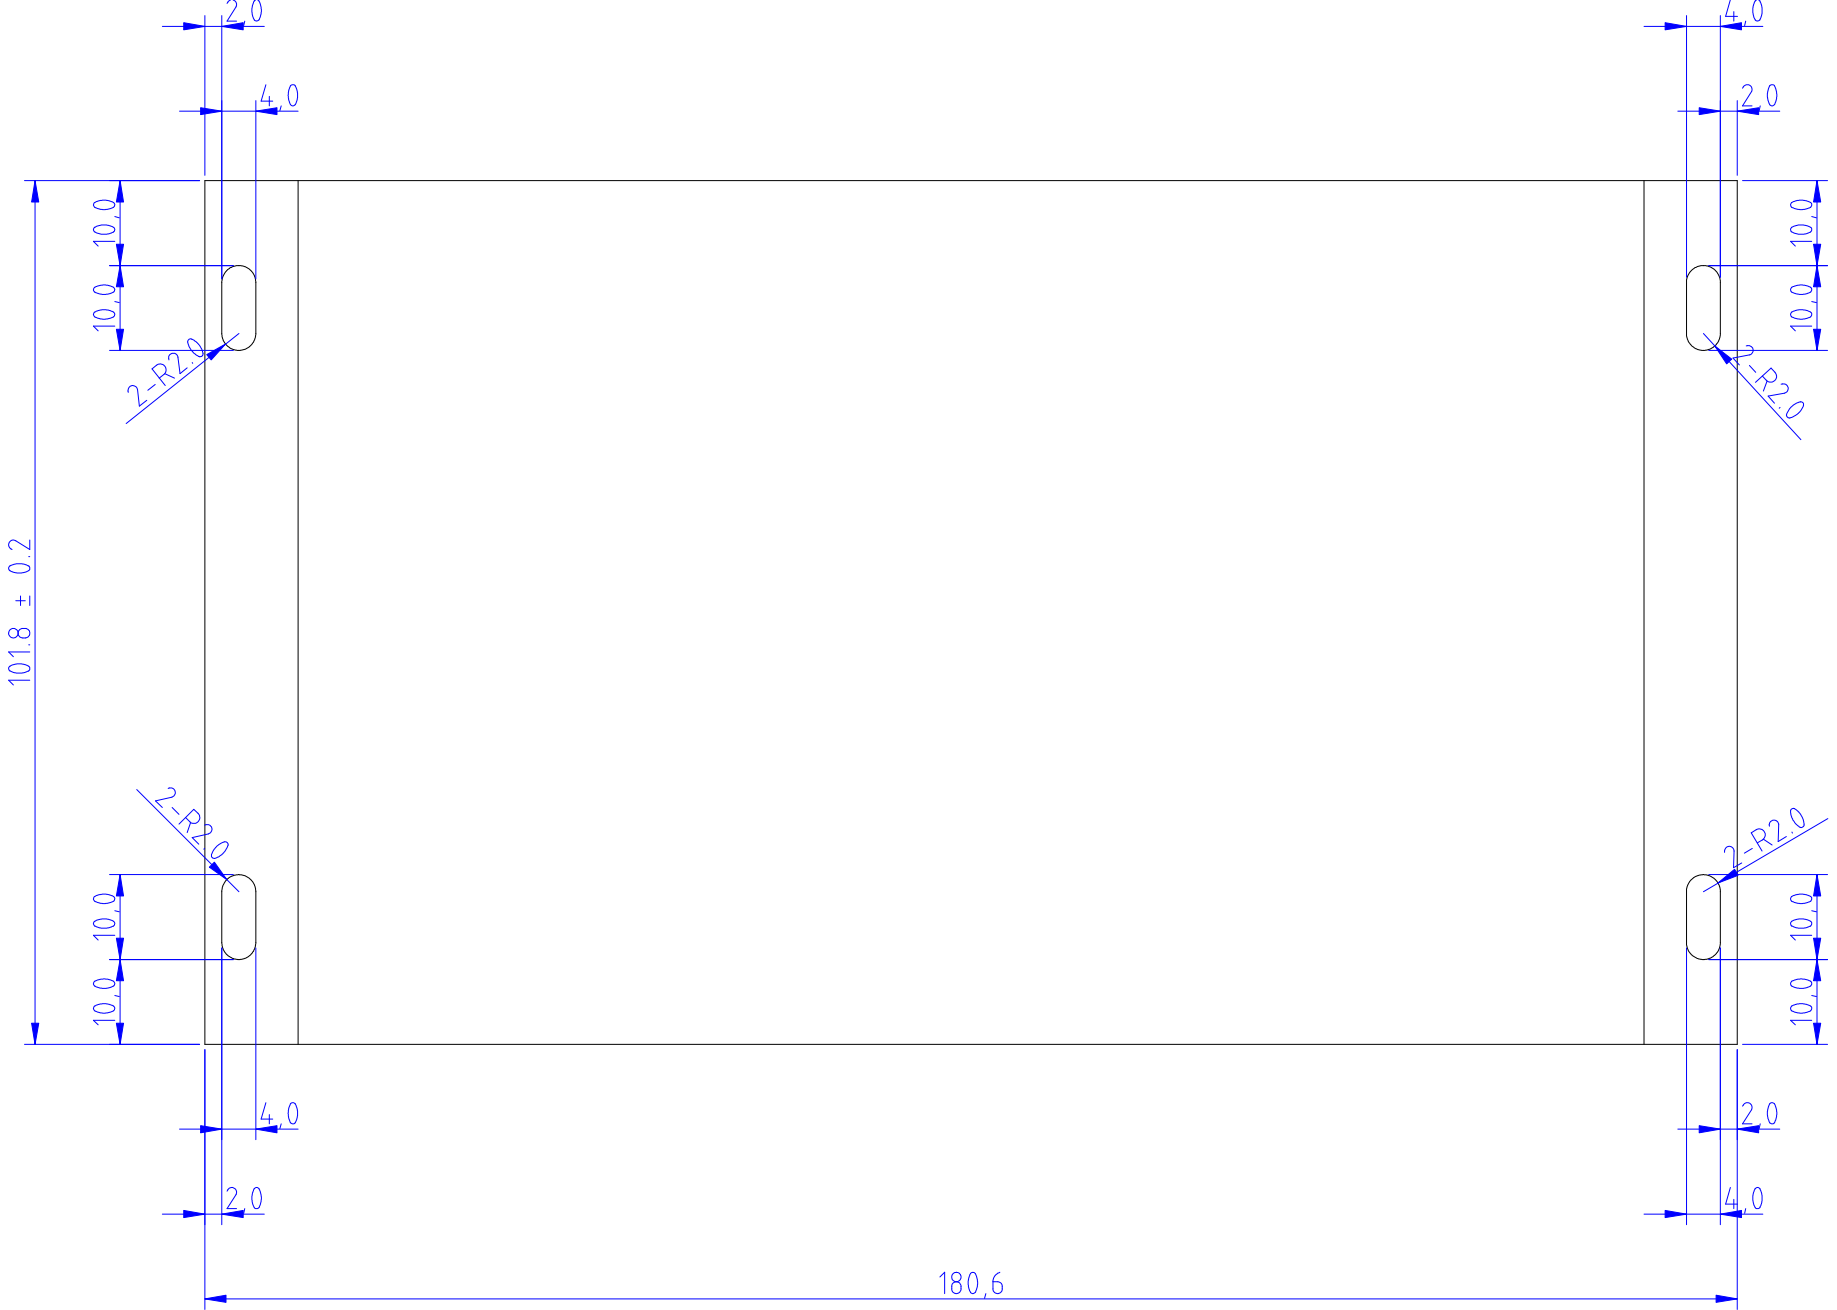
[picture p158: page 2]
