sparkfun/SparkFun_RTK_mosaic-X5/Test_Sketches/RTK_mosaic-X5_WiFi_STN_BT_Prov/main/fnt_5x8.h

/****************************************************************************** 
font5x7.h
Definition for small font

This file was imported from
https://github.com/sparkfun/SparkFun_Qwiic_OLED_Arduino_Library/blob/main/src/res/_fnt_5x7.h

which was imported from the MicroView library, written by GeekAmmo
(https://github.com/geekammo/MicroView-Arduino-Library), and released under 
the terms of the GNU General Public License as published by the Free Software 
Foundation, either version 3 of the License, or (at your option) any later 
version.

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
Modified by:
Emil Varughese @ Edwin Robotics Pvt. Ltd.
July 27, 2015
https://github.com/emil01/SparkFun_Micro_OLED_Arduino_Library/

******************************************************************************/
#pragma once 

// Define the font attributes
#define FONT_5X7_WIDTH        5
#define FONT_5X7_HEIGHT       8
#define FONT_5X7_START        0
#define FONT_5X7_NCHAR        255
#define FONT_5X7_MAP_WIDTH    1275
#define FONT_5X7_NAME         "5 x 7"

// Standard ASCII 5x7 font
	static const uint8_t font5x7_data[] = {
	0x00, 0x00, 0x00, 0x00, 0x00,
	0x3E, 0x5B, 0x4F, 0x5B, 0x3E,
	0x3E, 0x6B, 0x4F, 0x6B, 0x3E,
	0x1C, 0x3E, 0x7C, 0x3E, 0x1C,
	0x18, 0x3C, 0x7E, 0x3C, 0x18,
	0x1C, 0x57, 0x7D, 0x57, 0x1C,
	0x1C, 0x5E, 0x7F, 0x5E, 0x1C,
	0x00, 0x18, 0x3C, 0x18, 0x00,
	0xFF, 0xE7, 0xC3, 0xE7, 0xFF,
	0x00, 0x18, 0x24, 0x18, 0x00,
	0xFF, 0xE7, 0xDB, 0xE7, 0xFF,
	0x30, 0x48, 0x3A, 0x06, 0x0E,
	0x26, 0x29, 0x79, 0x29, 0x26,
	0x40, 0x7F, 0x05, 0x05, 0x07,
	0x40, 0x7F, 0x05, 0x25, 0x3F,
	0x5A, 0x3C, 0xE7, 0x3C, 0x5A,
	0x7F, 0x3E, 0x1C, 0x1C, 0x08,
	0x08, 0x1C, 0x1C, 0x3E, 0x7F,
	0x14, 0x22, 0x7F, 0x22, 0x14,
	0x5F, 0x5F, 0x00, 0x5F, 0x5F,
	0x06, 0x09, 0x7F, 0x01, 0x7F,
	0x00, 0x66, 0x89, 0x95, 0x6A,
	0x60, 0x60, 0x60, 0x60, 0x60,
	0x94, 0xA2, 0xFF, 0xA2, 0x94,
	0x08, 0x04, 0x7E, 0x04, 0x08,
	0x10, 0x20, 0x7E, 0x20, 0x10,
	0x08, 0x08, 0x2A, 0x1C, 0x08,
	0x08, 0x1C, 0x2A, 0x08, 0x08,
	0x1E, 0x10, 0x10, 0x10, 0x10,
	0x0C, 0x1E, 0x0C, 0x1E, 0x0C,
	0x30, 0x38, 0x3E, 0x38, 0x30,
	0x06, 0x0E, 0x3E, 0x0E, 0x06,
	0x00, 0x00, 0x00, 0x00, 0x00,
	0x00, 0x00, 0x5F, 0x00, 0x00,
	0x00, 0x07, 0x00, 0x07, 0x00,
	0x14, 0x7F, 0x14, 0x7F, 0x14,
	0x24, 0x2A, 0x7F, 0x2A, 0x12,
	0x23, 0x13, 0x08, 0x64, 0x62,
	0x36, 0x49, 0x56, 0x20, 0x50,
	0x00, 0x08, 0x07, 0x03, 0x00,
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
};
